Elecrow-RD/CrowPanel-5.0-HMI-ESP32-Display-800x480/example/V3.0/ESP_IDF/LVGL_Control_LED_50/components/Arduino_GFX-master/examples/ImgViewer/ImgViewerAnimatedGIF_GIFDEC/data/ezgif.com-optimize.gif

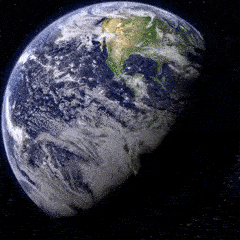
example/V3.0/ESP_IDF/LVGL_Control_LED_50/components/Arduino_GFX-master/examples/ImgViewer/ImgViewerAnimatedGIF_GIFDEC/data/ezgif.com-optimize.gif
