Elecrow-RD/CrowPanel-5.0-HMI-ESP32-Display-800x480/example/V3.0/ESP_IDF/LVGL_Control_LED_50/components/lvgl-9/docs/misc/perfetto_ui.png

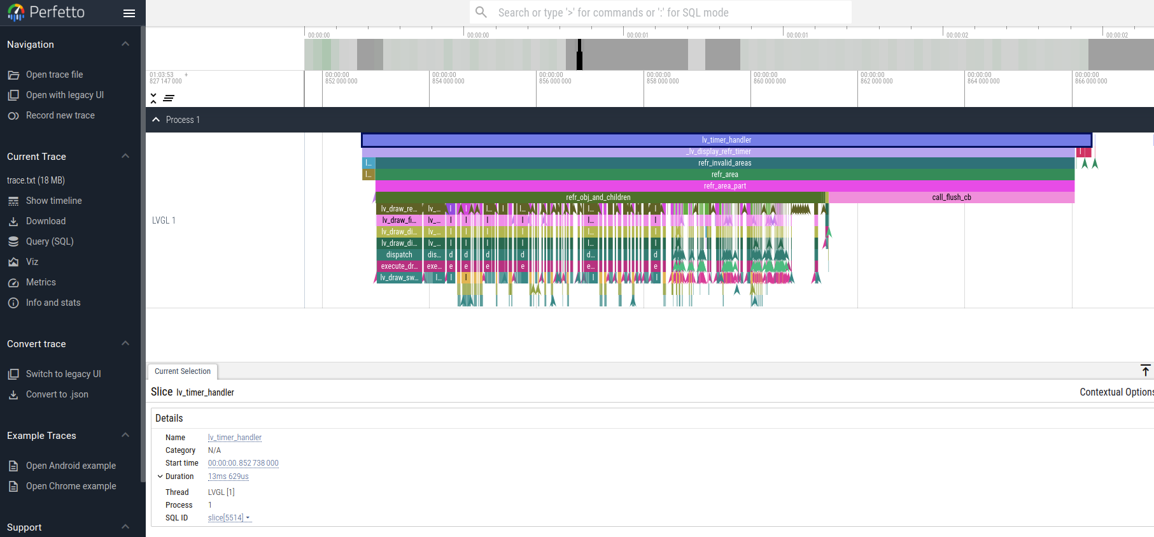
example/V3.0/ESP_IDF/LVGL_Control_LED_50/components/lvgl-9/docs/misc/perfetto_ui.png
