Elecrow-RD/CrowPanel-5.0-HMI-ESP32-Display-800x480/example/V1.0_and_V2.0/ESP_IDF/CrowPanel_ESP32_5.0/components/arduino-esp32-master/docs/source/make.rst

==============
makeEspArduino
==============

The `makeEspArduino <https://github.com/plerup/makeEspArduino>`_ is a generic makefile for any ESP8266/ESP32 Arduino project. 
Using it instead of the Arduino IDE makes it easier to do automated and production builds.
