Elecrow-RD/CrowPanel-5.0-HMI-ESP32-Display-800x480/example/V3.0/PlatformIO50/src/main.cpp

#include <Arduino.h>
#include <Wire.h>
#include <LovyanGFX.hpp>
#include <lgfx/v1/platforms/esp32s3/Bus_RGB.hpp>
#include <lgfx/v1/platforms/esp32s3/Panel_RGB.hpp>
#include <lvgl.h>

#include "dht20.h"
#include "touch.h"
#include "ui.h"

/*---------------------------------------------------------------
 * PlatformIO RGB/LVGL application
 * Configure the 800x480 panel, sensor, touch input, and generated UI.
 *--------------------------------------------------------------*/
namespace {
// These values bind LVGL and the application outputs to the 5.0-inch board.
constexpr uint16_t screen_width = 800;
constexpr uint16_t screen_height = 480;
constexpr uint8_t backlight_pin = 2;
constexpr uint8_t led_pin = 38;

class Display : public lgfx::LGFX_Device {
public:
    lgfx::Bus_RGB bus;
    lgfx::Panel_RGB panel;

    /** Configure RGB timing, data pins, and the 800x480 panel. */
    Display()
    {
        // Configure the RGB data bus and verified synchronization timings.
        auto bus_config = bus.config();
        bus_config.panel = &panel;
        const int8_t data_pins[16] = {8, 3, 46, 9, 1, 5, 6, 7, 15, 16, 4, 45, 48, 47, 21, 14};
        memcpy(bus_config.pin_data, data_pins, sizeof(data_pins));
        bus_config.pin_henable = 40;
        bus_config.pin_vsync = 41;
        bus_config.pin_hsync = 39;
        bus_config.pin_pclk = 0;
        bus_config.freq_write = 12000000;
        bus_config.hsync_polarity = 0;
        bus_config.hsync_front_porch = 8;
        bus_config.hsync_pulse_width = 4;
        bus_config.hsync_back_porch = 43;
        bus_config.vsync_polarity = 0;
        bus_config.vsync_front_porch = 8;
        bus_config.vsync_pulse_width = 4;
        bus_config.vsync_back_porch = 12;
        bus_config.pclk_active_neg = 1;
        bus_config.de_idle_high = 0;
        bus_config.pclk_idle_high = 0;
        bus.config(bus_config);

        // Keep the frame-buffer geometry equal to the physical panel size.
        auto panel_config = panel.config();
        panel_config.memory_width = screen_width;
        panel_config.memory_height = screen_height;
        panel_config.panel_width = screen_width;
        panel_config.panel_height = screen_height;
        panel.config(panel_config);
        panel.setBus(&bus);
        setPanel(&panel);
    }
};

Display lcd;

/** Return the millisecond time base consumed by LVGL. */
uint32_t lvgl_tick()
{
    return millis();
}

/** Present the full RGB frame buffer selected by LovyanGFX. */
void display_flush(lv_display_t * display, const lv_area_t *, uint8_t * pixel_map)
{
    // Present the full buffer at VSYNC, then let LVGL render the next frame.
    if (!lcd.bus.presentFrameBuffer(pixel_map)) {
        Serial.println("Display frame switch timeout");
    }
    lv_display_flush_ready(display);
}

/** Supply the latest GT911 point and log each new press. */
void touch_read(lv_indev_t *, lv_indev_data_t * data)
{
    static int16_t last_x = 0;
    static int16_t last_y = 0;
    static bool was_pressed = false;
    // Preserve the last coordinates while exposing the current press state.
    const bool pressed = touch_read_point(last_x, last_y);
    data->state = pressed ? LV_INDEV_STATE_PRESSED : LV_INDEV_STATE_RELEASED;
    data->point.x = last_x;
    data->point.y = last_y;
    // Log only the transition into a press to avoid flooding the serial port.
    if (pressed && !was_pressed) {
        Serial.printf("Touch %d,%d\n", last_x, last_y);
    }
    was_pressed = pressed;
}

/** Apply the generated UI's LED request to GPIO 38. */
void set_led(bool enabled)
{
    digitalWrite(led_pin, enabled ? HIGH : LOW);
}

}

/**
 * @brief Initialize hardware, LVGL callbacks, and generated UI.
 *
 * Called once after reset; the serial log identifies each major subsystem.
 */
void setup()
{
    Serial.begin(115200);
    Wire.begin(19, 20);
    pinMode(led_pin, OUTPUT);
    set_led(false);

    if (!lcd.begin()) {
        Serial.println("LovyanGFX lcd.begin() failed");
        return;
    }
    Serial.println("LovyanGFX lcd.begin() OK");
    delay(200);
    pinMode(backlight_pin, OUTPUT);
    digitalWrite(backlight_pin, HIGH);

    lv_init();
    lv_tick_set_cb(lvgl_tick);
    delay(100);

    touch_init();
    Serial.println(dht20_init() ? "DHT20 ready" : "DHT20 not found");

    // Attach LovyanGFX's two full frames so LVGL can swap them at VSYNC.
    lv_color_t * frame_buffer_0 = reinterpret_cast<lv_color_t *>(lcd.bus.getFrameBuffer(0));
    lv_color_t * frame_buffer_1 = reinterpret_cast<lv_color_t *>(lcd.bus.getFrameBuffer(1));
    lv_display_t * display = lv_display_create(screen_width, screen_height);
    lv_display_set_color_format(display, LV_COLOR_FORMAT_RGB565);
    lv_display_set_flush_cb(display, display_flush);
    lv_display_set_buffers(display, frame_buffer_0, frame_buffer_1,
                           screen_width * screen_height * sizeof(lv_color_t),
                           LV_DISPLAY_RENDER_MODE_FULL);

    // Register GT911 as LVGL's pointer source for generated UI widgets.
    lv_indev_t * touch = lv_indev_create();
    lv_indev_set_type(touch, LV_INDEV_TYPE_POINTER);
    lv_indev_set_read_cb(touch, touch_read);

    ui_init(set_led);
    lv_timer_handler();
    Serial.printf("Ready: Arduino %s, LVGL %d.%d.%d\n", ESP_ARDUINO_VERSION_STR,
                  LVGL_VERSION_MAJOR, LVGL_VERSION_MINOR, LVGL_VERSION_PATCH);
}

/**
 * @brief Refresh DHT20 labels once per second and service LVGL continuously.
 */
void loop()
{
    static uint32_t last_sensor_read = 0;
    const uint32_t now = millis();
    // Read the DHT20 once per second while servicing LVGL every iteration.
    if (now - last_sensor_read >= 1000) {
        last_sensor_read = now;
        int temperature;
        int humidity;
        if (dht20_read(temperature, humidity)) {
            lv_label_set_text_fmt(ui_TempLabel, "%d", temperature);
            lv_label_set_text_fmt(ui_HumiLabel, "%d", humidity);
            Serial.printf("DHT20: %d C, %d %%\n", temperature, humidity);
        } else {
            Serial.println("DHT20 read failed");
        }
    }
    lv_timer_handler();
    delay(5);
}
