Elecrow-RD/CrowPanel-5.0-HMI-ESP32-Display-800x480/example/V3.0/Arduino/Course/LVGL_Arduino5.0/ui_img_on_png.c

// Generated image module: stores the LED-on button image in flash.
// SquareLine Studio version: SquareLine Studio 1.5.1
// LVGL version: 9.1.0
// Project name: Basic_LVGL_7-5

#include "ui.h"

#ifndef LV_ATTRIBUTE_MEM_ALIGN
    #define LV_ATTRIBUTE_MEM_ALIGN
#endif

// IMAGE DATA: assets/on.png
const LV_ATTRIBUTE_MEM_ALIGN uint8_t ui_img_on_png_data[] = {
    0xFF,0xFF,0xFF,0xFF,0xFF,0xFF,0xFF,0xFF,0xFF,0x87,0xFF,0x87,0xFF,0x87,0xFF,0x87,0xFF,0x87,0xFF,0x87,0xFF,0x87,0xFF,0x87,0xFF,0x87,0xFF,0x87,0xFF,0x87,0xFF,0x87,0xFF,0x87,0xFF,0x87,0xFF,0x87,0xFF,0x87,0xFF,0x87,0xFF,0x87,0xFF,0x87,0xFF,0x87,0xFF,0x87,0xFF,0x87,0xFF,0x87,0xFF,0x87,0xFF,0x87,0xFF,0x87,0xFF,0x87,0xFF,0x87,0xFF,0x87,0xFF,0x87,0xFF,0x87,0xFF,0x87,0xFF,0x87,0xFF,0x87,0xFF,0x87,0xFF,0x87,0xFF,0x87,0xFF,0x87,0xFF,0x87,0xFF,0x87,0xFF,0x87,0xFF,0x87,0xFF,0x87,0xFF,0x87,0xFF,0x87,0xFF,0x87,0xFF,0x87,0xFF,0x87,0xFF,0x87,0xFF,0x87,0xFF,0x87,0xFF,0x87,0xFF,0x87,0xFF,0x87,0xFF,0x87,0xFF,0x87,0xFF,0x87,0xFF,0x87,0xFF,0x87,0xFF,0x87,
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
};
const lv_image_dsc_t ui_img_on_png = {
    .header.w = 80,
    .header.h = 79,
    .data_size = sizeof(ui_img_on_png_data),
    .header.cf = LV_COLOR_FORMAT_NATIVE_WITH_ALPHA,
    .header.magic = LV_IMAGE_HEADER_MAGIC,
    .data = ui_img_on_png_data
};
