Elecrow-RD/CrowPanel-5.0-HMI-ESP32-Display-800x480/example/V3.0/PlatformIO50/include/touch.h

#pragma once

#include <stdint.h>

/** Initialize and probe the GT911 controller. */
void touch_init();
/** Read one mapped point; returns false when no finger is active. */
bool touch_read_point(int16_t & x, int16_t & y);
